HurleyResearch/nRFICE/fpga/ebr8x16/testbench/dut_params.v

localparam FAMILY = "iCE40UP";
localparam MEM_ID = "ebr8x16";
localparam MEM_SIZE = "16,256";
localparam ADDR_DEPTH = 256;
localparam DATA_WIDTH = 16;
localparam ADDR_WIDTH = 8;
localparam REGMODE = "reg";
localparam OUTPUT_CLK_EN = 0;
localparam RESETMODE = "sync";
localparam BYTE_ENABLE = 0;
localparam BYTE_WIDTH = 2;
localparam BYTE_SIZE = 8;
localparam WRITE_MODE = "normal";
localparam ECC_ENABLE = 0;
localparam INIT_MODE = "none";
localparam INIT_FILE = "none";
localparam INIT_FILE_FORMAT = "hex";
localparam INIT_VALUE_00 = "0x0000000000000000000000000000000000000000000000000000000000000000";
localparam INIT_VALUE_01 = "0x0000000000000000000000000000000000000000000000000000000000000000";
localparam INIT_VALUE_02 = "0x0000000000000000000000000000000000000000000000000000000000000000";
localparam INIT_VALUE_03 = "0x0000000000000000000000000000000000000000000000000000000000000000";
localparam INIT_VALUE_04 = "0x0000000000000000000000000000000000000000000000000000000000000000";
localparam INIT_VALUE_05 = "0x0000000000000000000000000000000000000000000000000000000000000000";
localparam INIT_VALUE_06 = "0x0000000000000000000000000000000000000000000000000000000000000000";
localparam INIT_VALUE_07 = "0x0000000000000000000000000000000000000000000000000000000000000000";
localparam INIT_VALUE_08 = "0x0000000000000000000000000000000000000000000000000000000000000000";
localparam INIT_VALUE_09 = "0x0000000000000000000000000000000000000000000000000000000000000000";
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
localparam INIT_VALUE_7E = "0x0000000000000000000000000000000000000000000000000000000000000000";
localparam INIT_VALUE_7F = "0x0000000000000000000000000000000000000000000000000000000000000000";
`define iCE40UP
`define ice40tp
`define iCE40UP5K
