HurleyResearch/nRFICE/fpga/ebr8x16/testbench/dut_inst.v

    ebr8x16 u_ebr8x16(.clk_i(clk_i),
        .rst_i(rst_i),
        .clk_en_i(clk_en_i),
        .wr_en_i(wr_en_i),
        .wr_data_i(wr_data_i),
        .addr_i(addr_i),
        .rd_data_o(rd_data_o));
